antmicro/lpddr4-test-board/assets/previews/layer0.webp

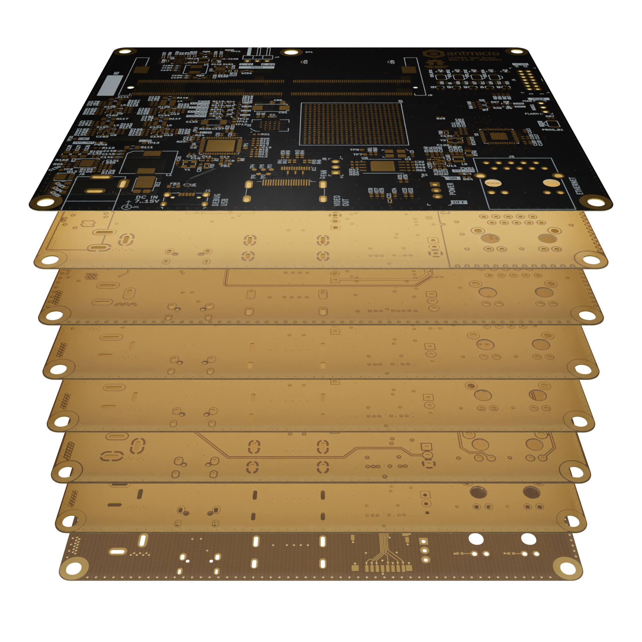
assets/previews/layer0.webp
