antmicro/lpddr4-test-board/assets/previews/layer0_thumbnail.png

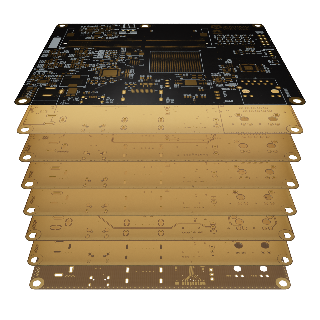
assets/previews/layer0_thumbnail.png
