antmicro/lpddr4-test-board/assets/previews/layer2.png

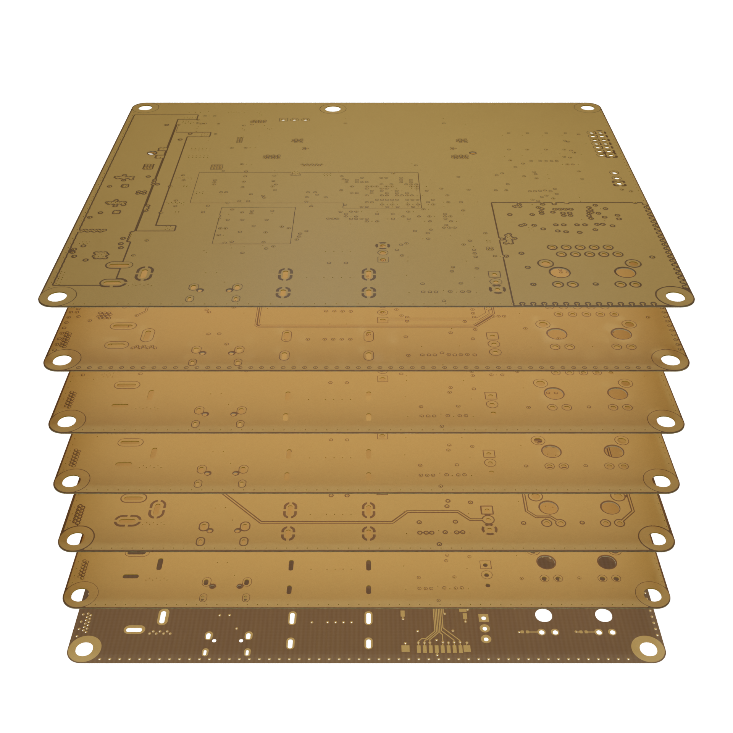
assets/previews/layer2.png
