antmicro/lpddr4-test-board/assets/previews/layer2_thumbnail.png

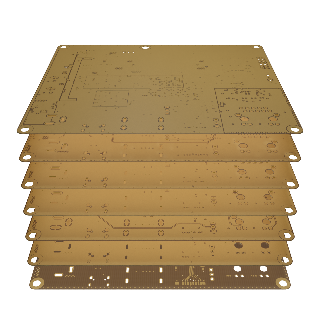
assets/previews/layer2_thumbnail.png
