antmicro/lpddr4-test-board/assets/previews/layer4.png

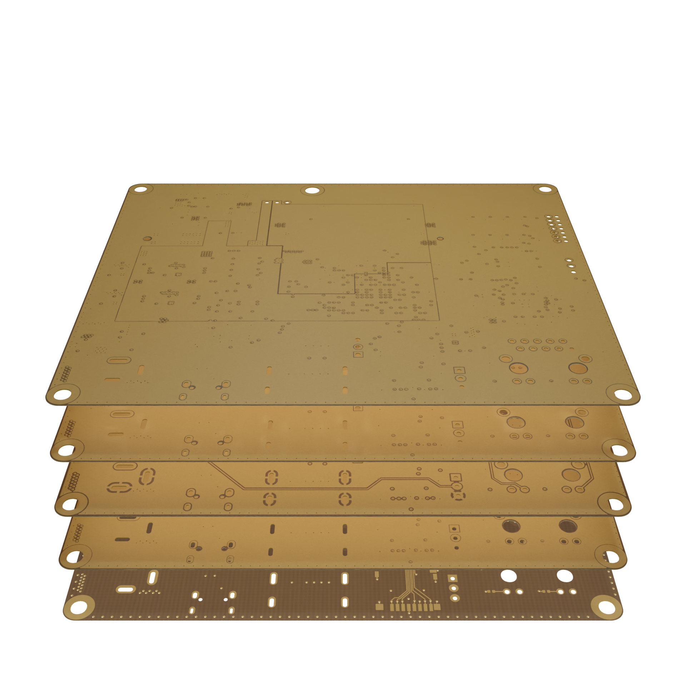
assets/previews/layer4.png
