antmicro/lpddr4-test-board/assets/previews/layer7.png

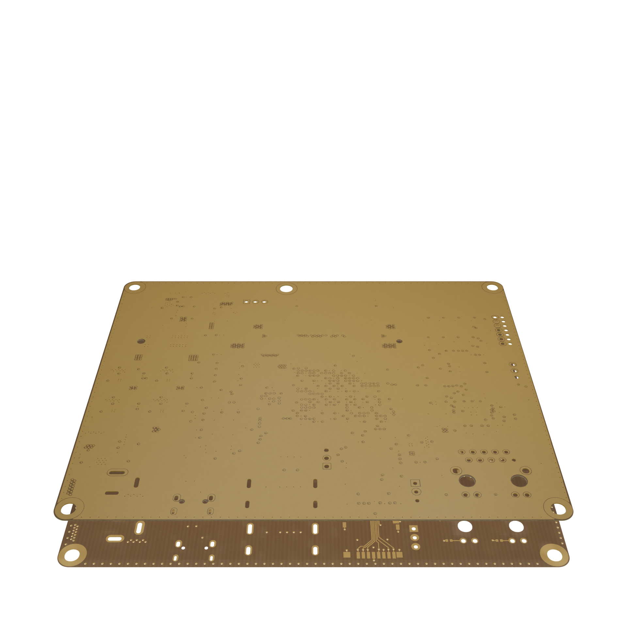
assets/previews/layer7.png
