antmicro/lpddr4-test-board/assets/previews/layer8.png

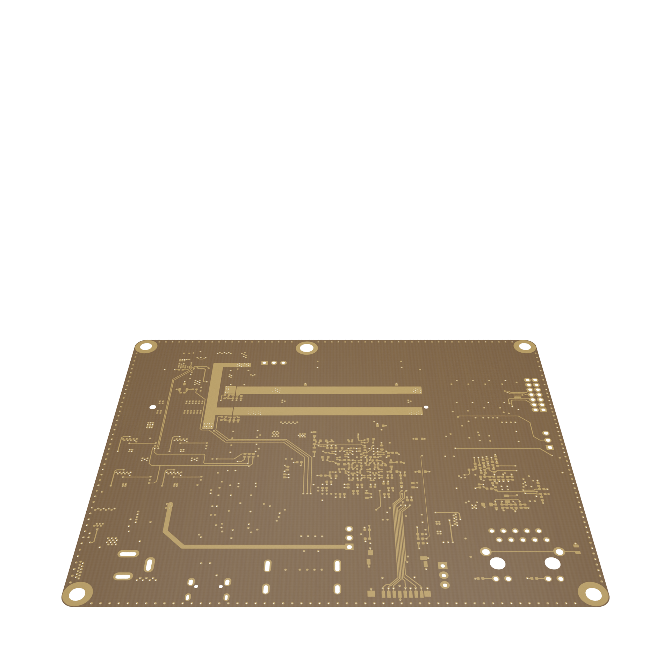
assets/previews/layer8.png
