antmicro/lpddr4-test-board/assets/previews/leftB.png

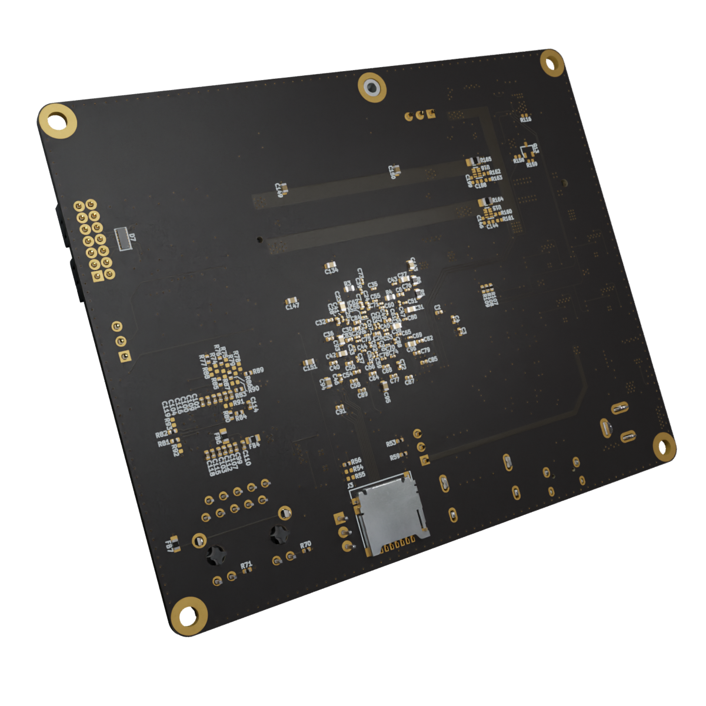
assets/previews/leftB.png
