antmicro/lpddr4-test-board/assets/previews/leftT.png

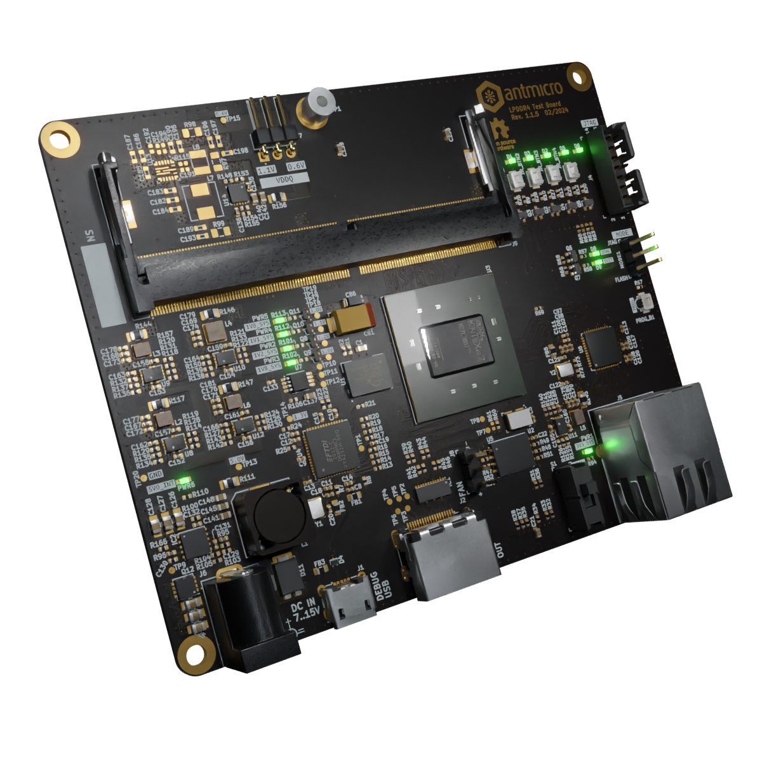
assets/previews/leftT.png
