antmicro/lpddr4-test-board/assets/previews/orthoB.png

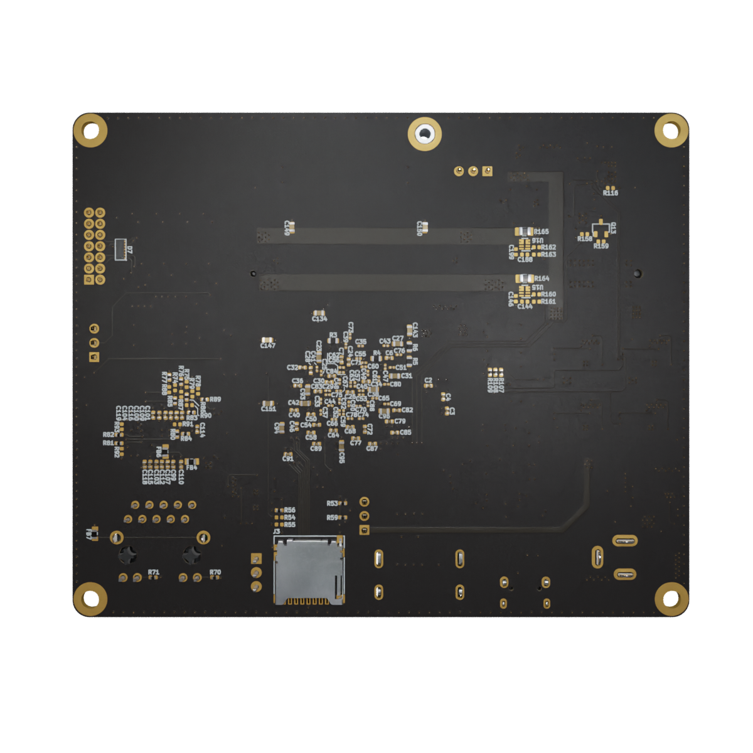
assets/previews/orthoB.png
