antmicro/lpddr4-test-board/assets/previews/orthoT.png

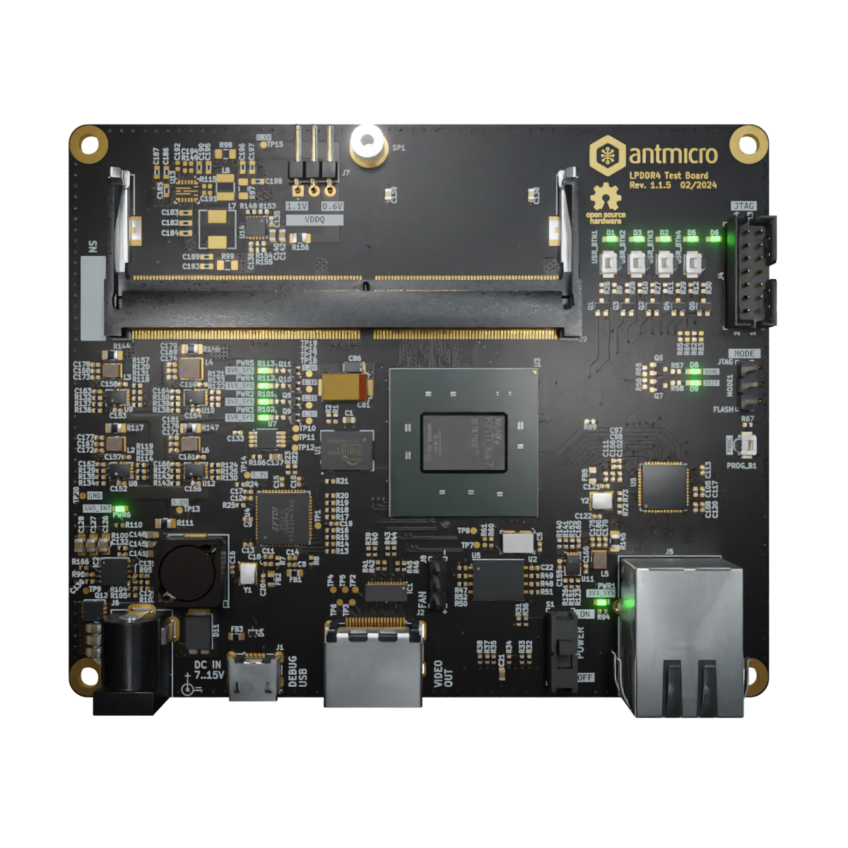
assets/previews/orthoT.png
