antmicro/lpddr4-test-board/assets/previews/photoB.png

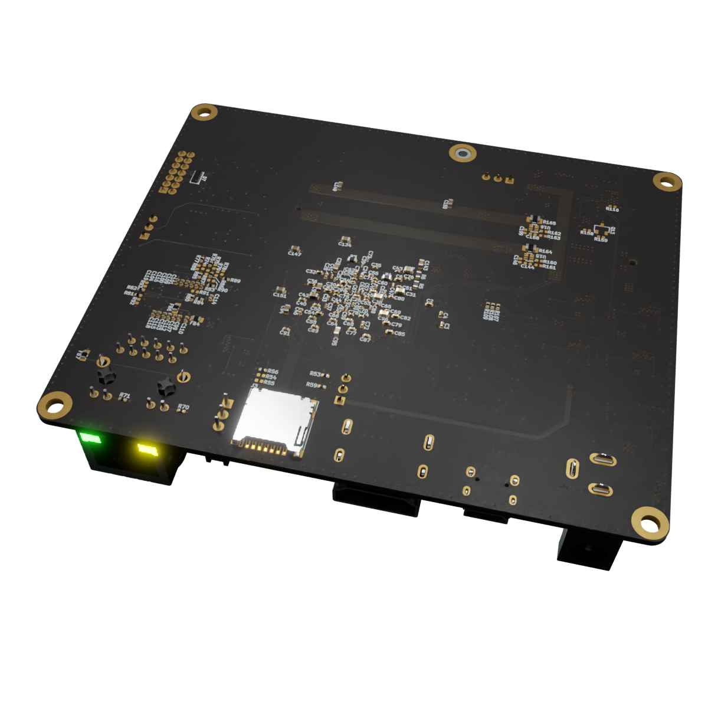
assets/previews/photoB.png
