antmicro/lpddr4-test-board/assets/previews/photoT.png

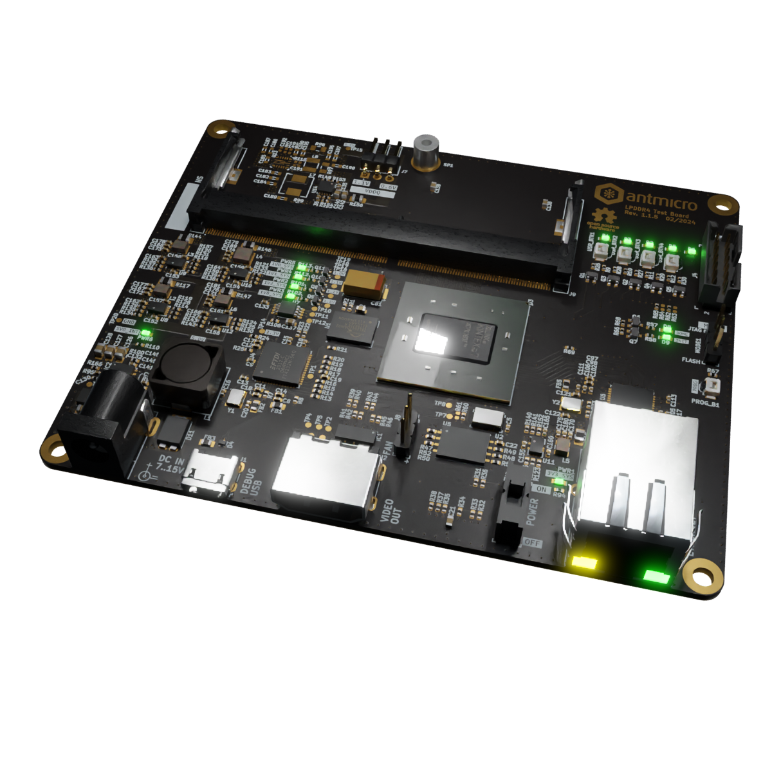
assets/previews/photoT.png
