antmicro/lpddr4-test-board/assets/previews/rightB.png

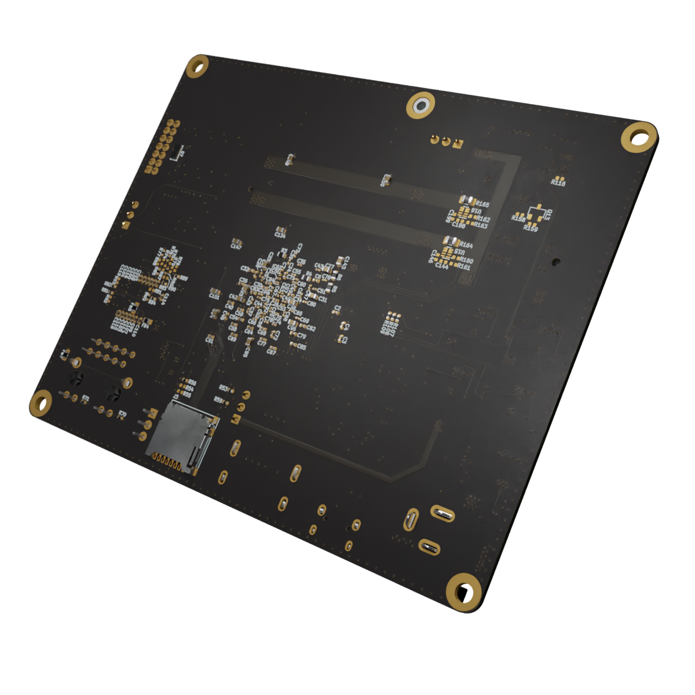
assets/previews/rightB.png
