antmicro/lpddr4-test-board/assets/previews/rightT.png

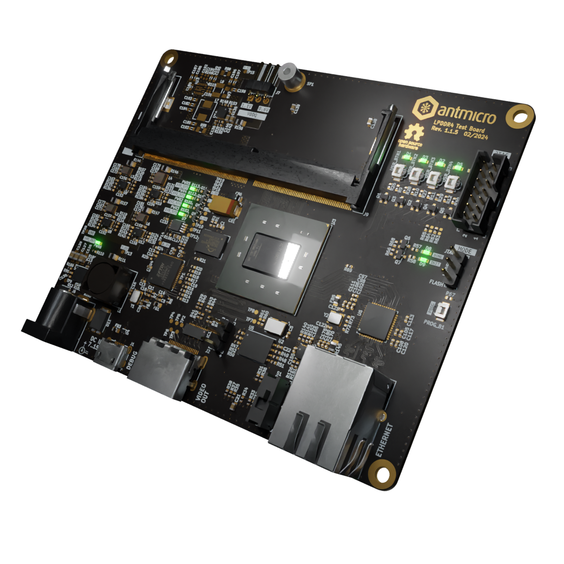
assets/previews/rightT.png
